kellervater/homeracker/png_creation/PXL_20250915_172044293.jpg

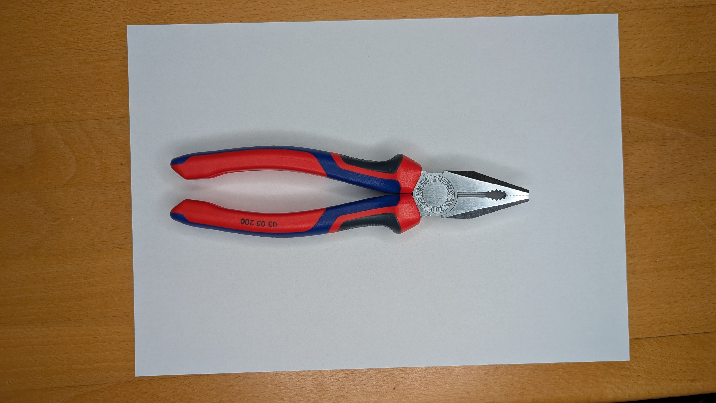
png_creation/PXL_20250915_172044293.jpg
