kellervater/homeracker/models/core/test/lockpin.scad

// HomeRacker - Lock Pin Test
//
// Test file for lock pin module.

// Use the main homeracker library file
include <../main.scad>

grip_type = "standard";
lockpin(grip_type=grip_type);
